froeca/Software-Defined-Radio/Images/Arduino_design.PNG

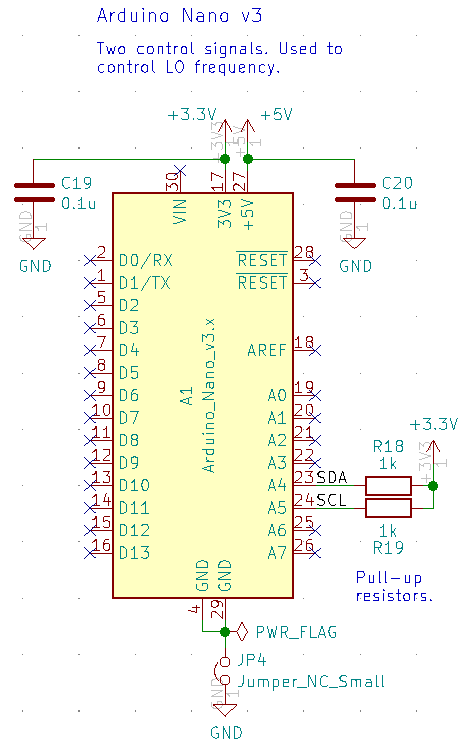
Images/Arduino_design.PNG
