froeca/Software-Defined-Radio/Images/BJT_design_v3a.PNG

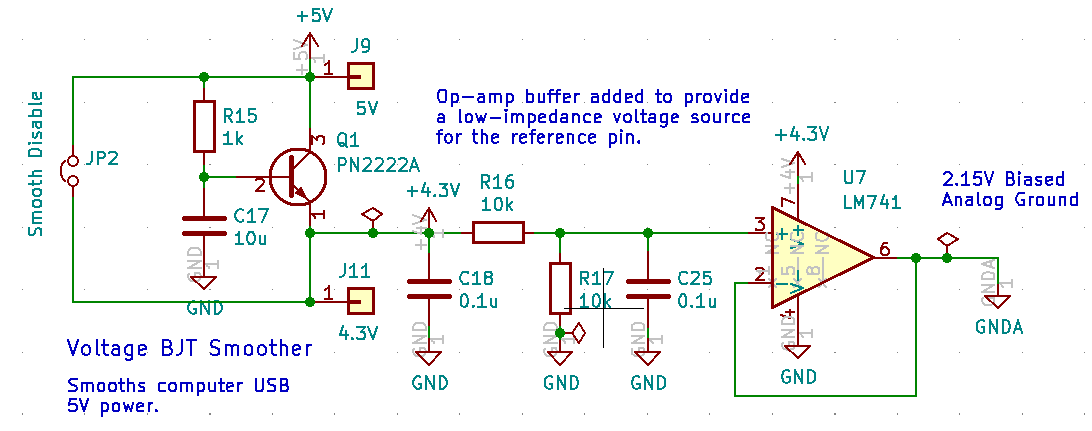
Images/BJT_design_v3a.PNG
