froeca/Software-Defined-Radio/Images/Block_Diagram.png

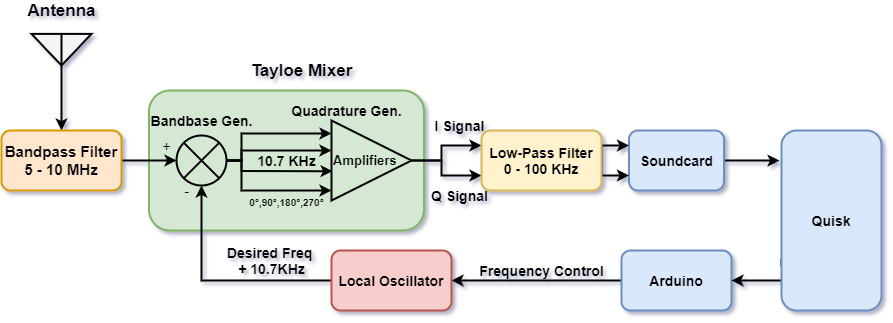
Images/Block_Diagram.png
