froeca/Software-Defined-Radio/Images/BPF_error.png

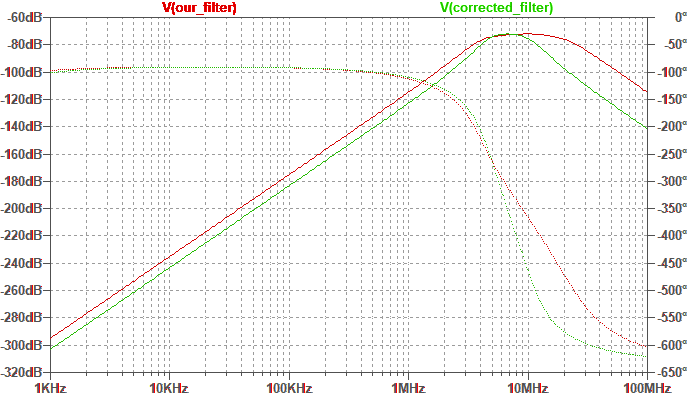
Images/BPF_error.png
