froeca/Software-Defined-Radio/Images/BPF_ideal.PNG

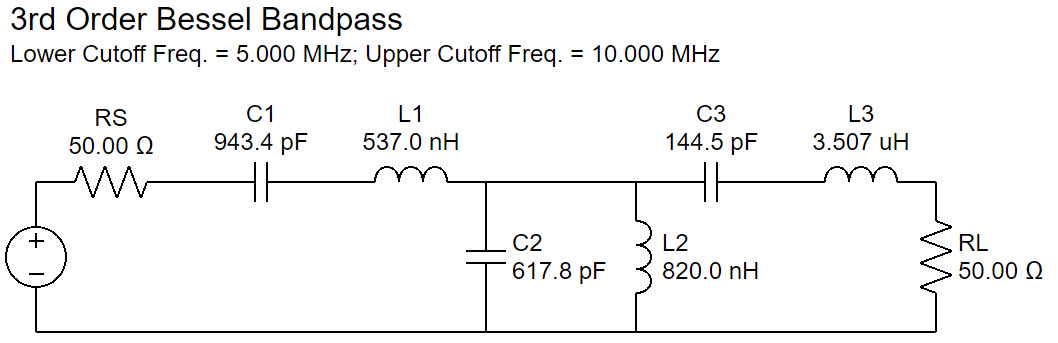
Images/BPF_ideal.PNG
