froeca/Software-Defined-Radio/Images/BPF_response.png

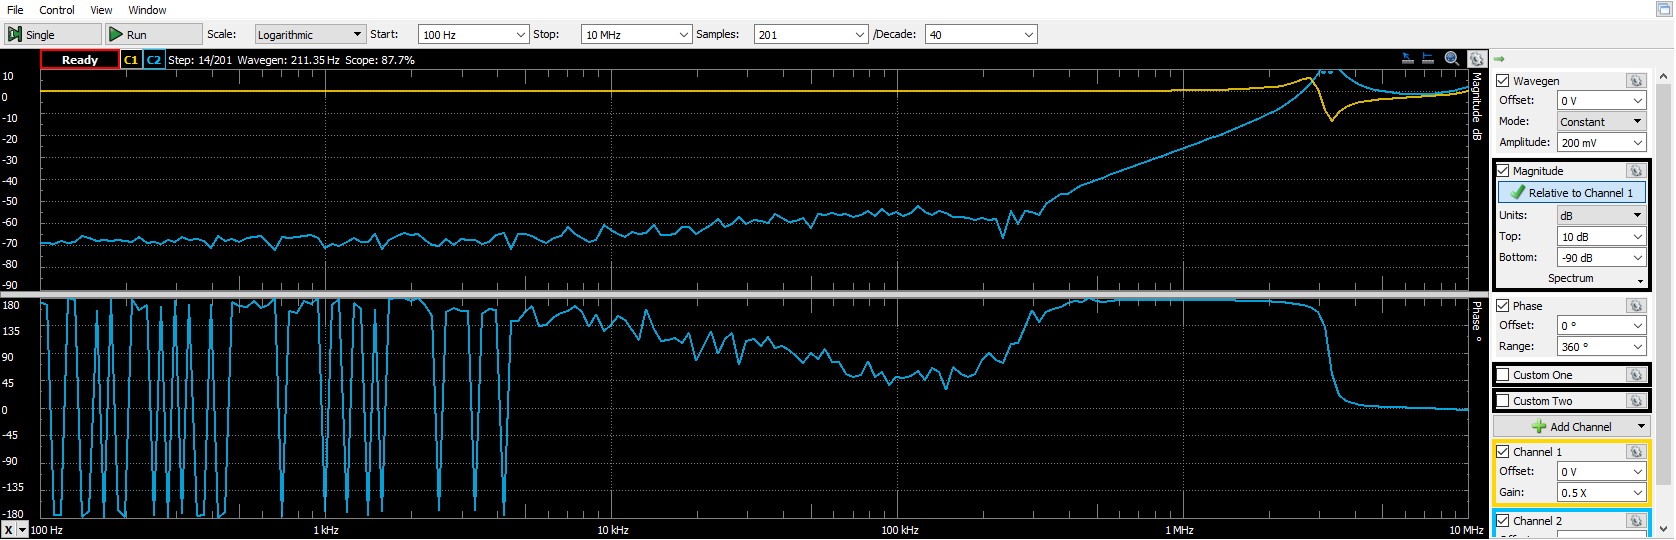
Images/BPF_response.png
