froeca/Software-Defined-Radio/Images/BPF_response_graph.PNG

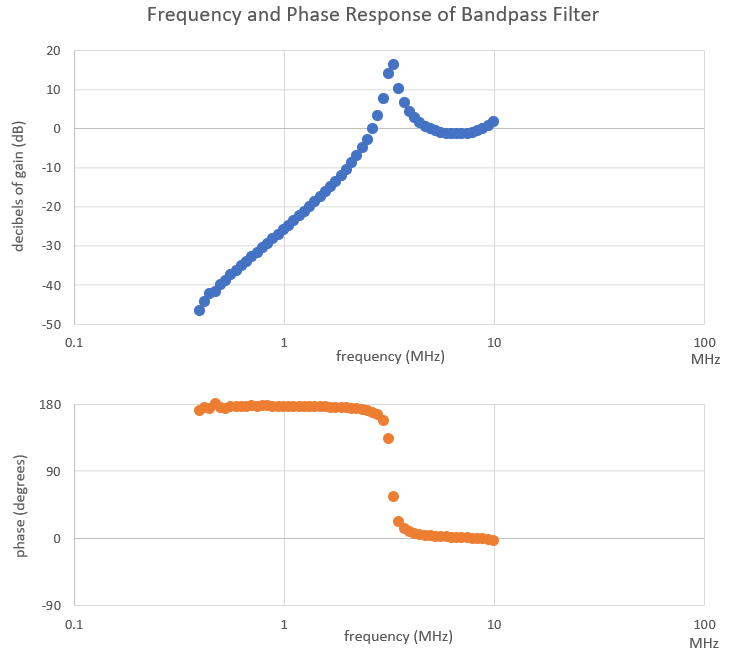
Images/BPF_response_graph.PNG
