froeca/Software-Defined-Radio/Images/Clkgen_response.jpeg

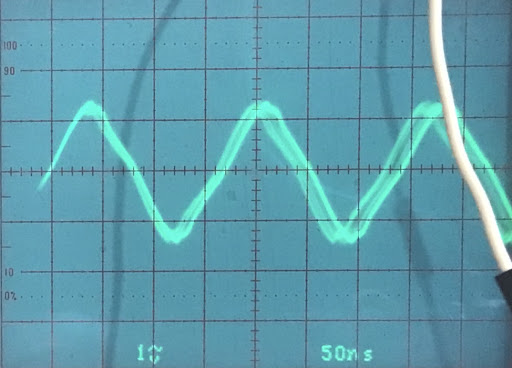
Images/Clkgen_response.jpeg
