froeca/Software-Defined-Radio/Images/Froelich_Reciever_PCB.png

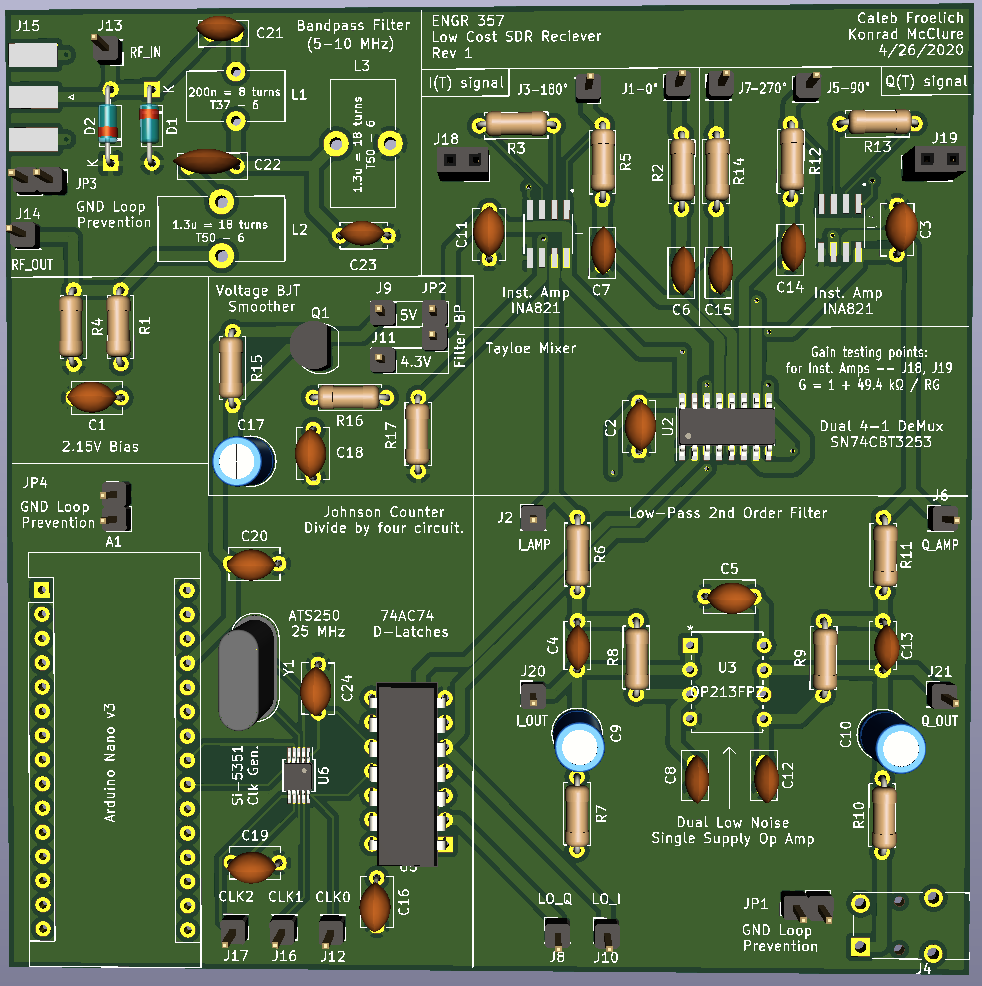
Images/Froelich_Reciever_PCB.png
