froeca/Software-Defined-Radio/Images/Froelich_Reciever_PCB_2.png

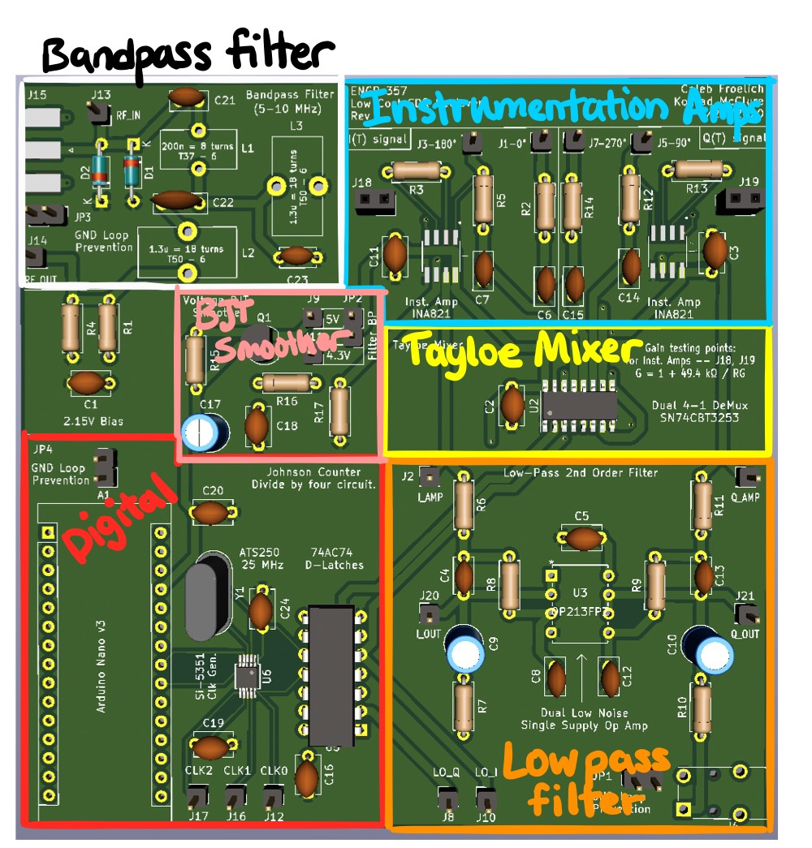
Images/Froelich_Reciever_PCB_2.png
