froeca/Software-Defined-Radio/Images/INA821_response.PNG

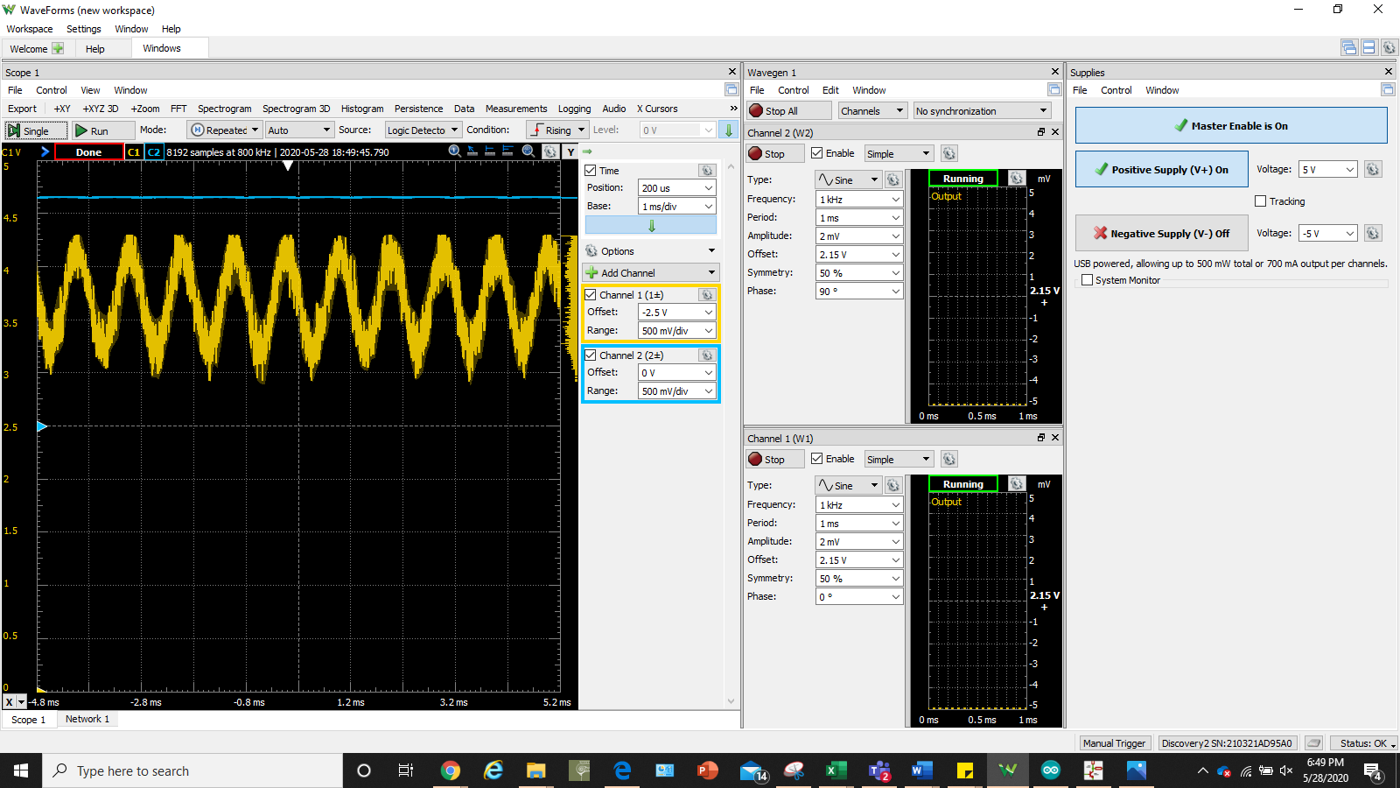
Images/INA821_response.PNG
