froeca/Software-Defined-Radio/Images/JCNTR_design.PNG

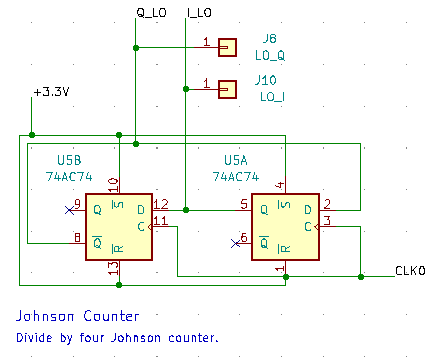
Images/JCNTR_design.PNG
