froeca/Software-Defined-Radio/Images/JCNTR_response2.jpeg

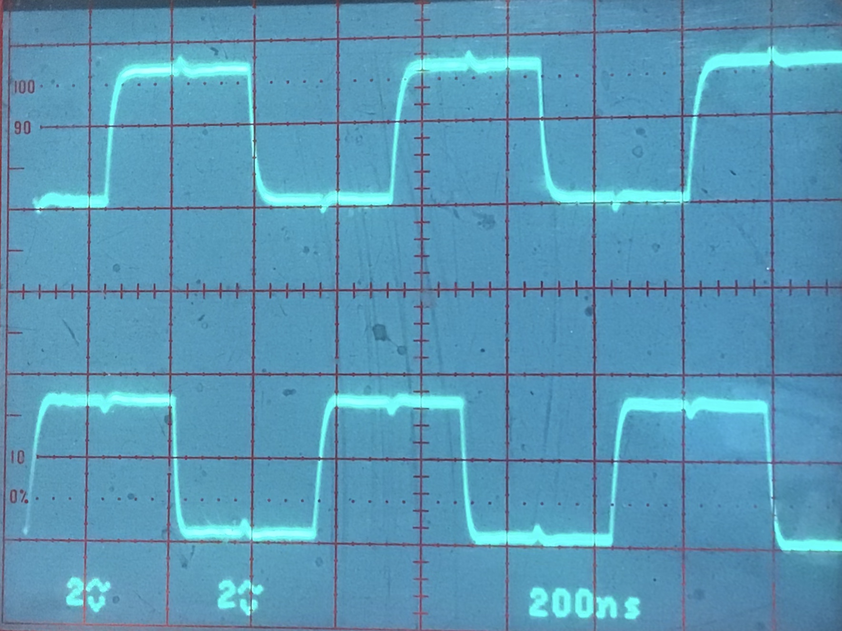
Images/JCNTR_response2.jpeg
