froeca/Software-Defined-Radio/Images/JCNTR_response.png

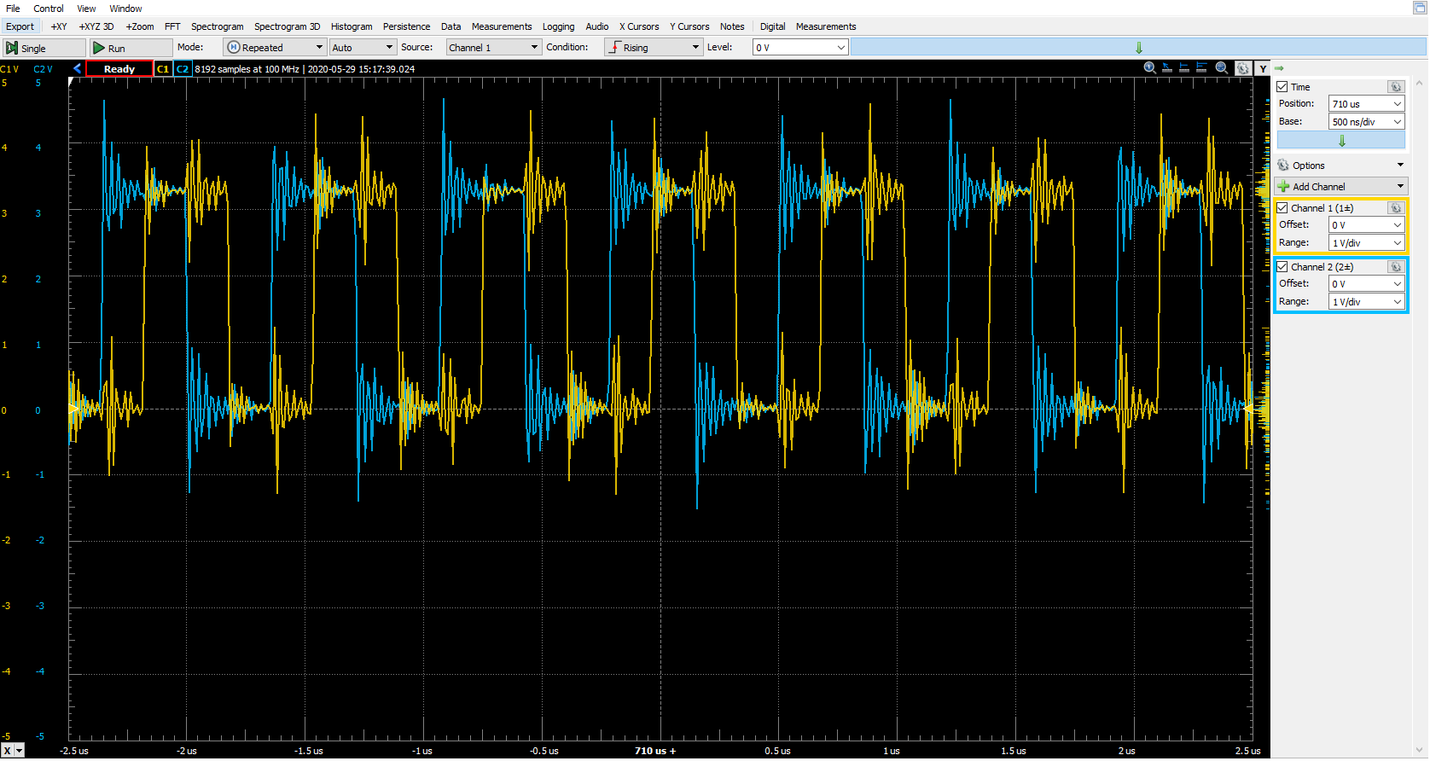
Images/JCNTR_response.png
