froeca/Software-Defined-Radio/Images/LPF_design.PNG

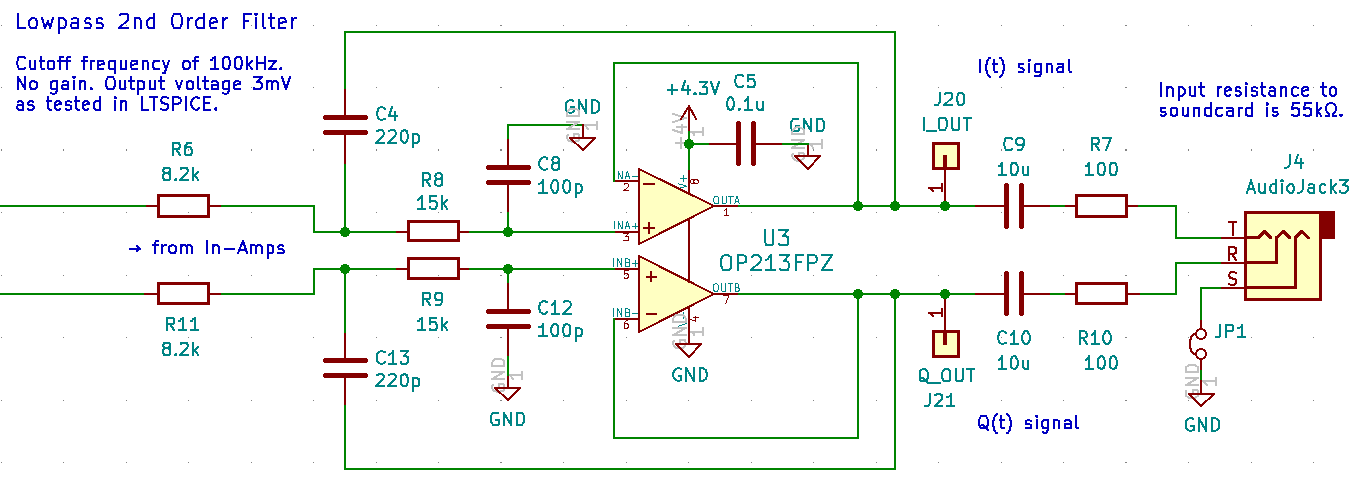
Images/LPF_design.PNG
