froeca/Software-Defined-Radio/Images/LPF_response.png

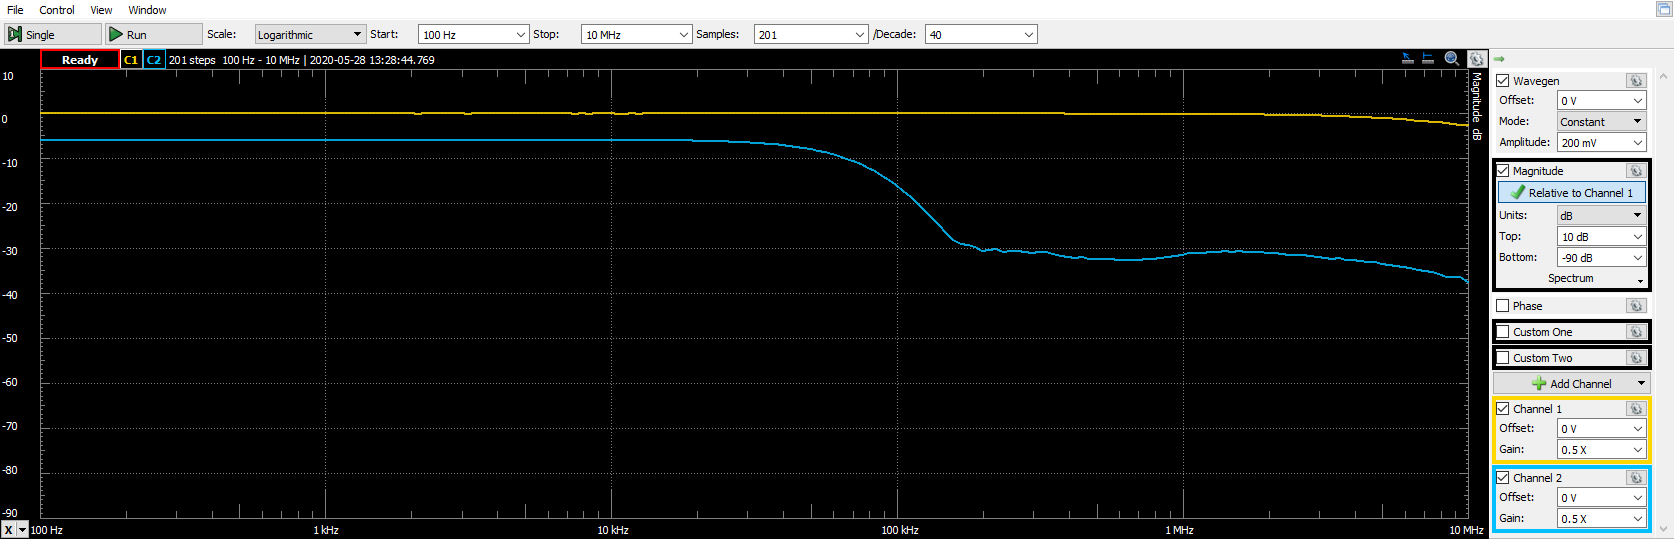
Images/LPF_response.png
