froeca/Software-Defined-Radio/Images/LPF_response_graph.PNG

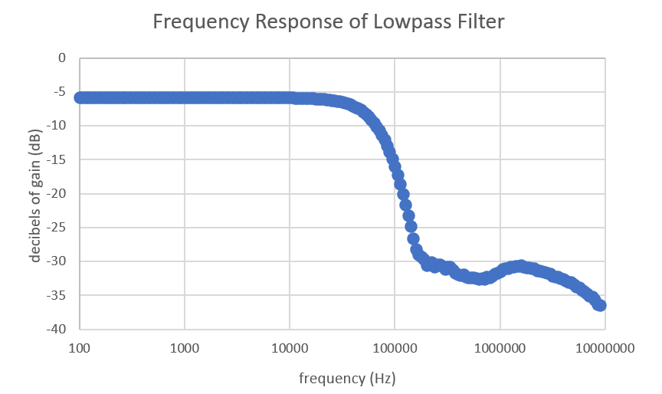
Images/LPF_response_graph.PNG
