froeca/Software-Defined-Radio/Images/Pull-up_Resistors.jpg

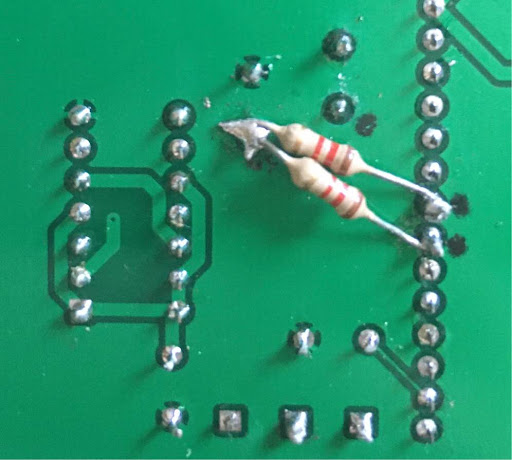
Images/Pull-up_Resistors.jpg
