froeca/Software-Defined-Radio/Images/SDA_SCL.png

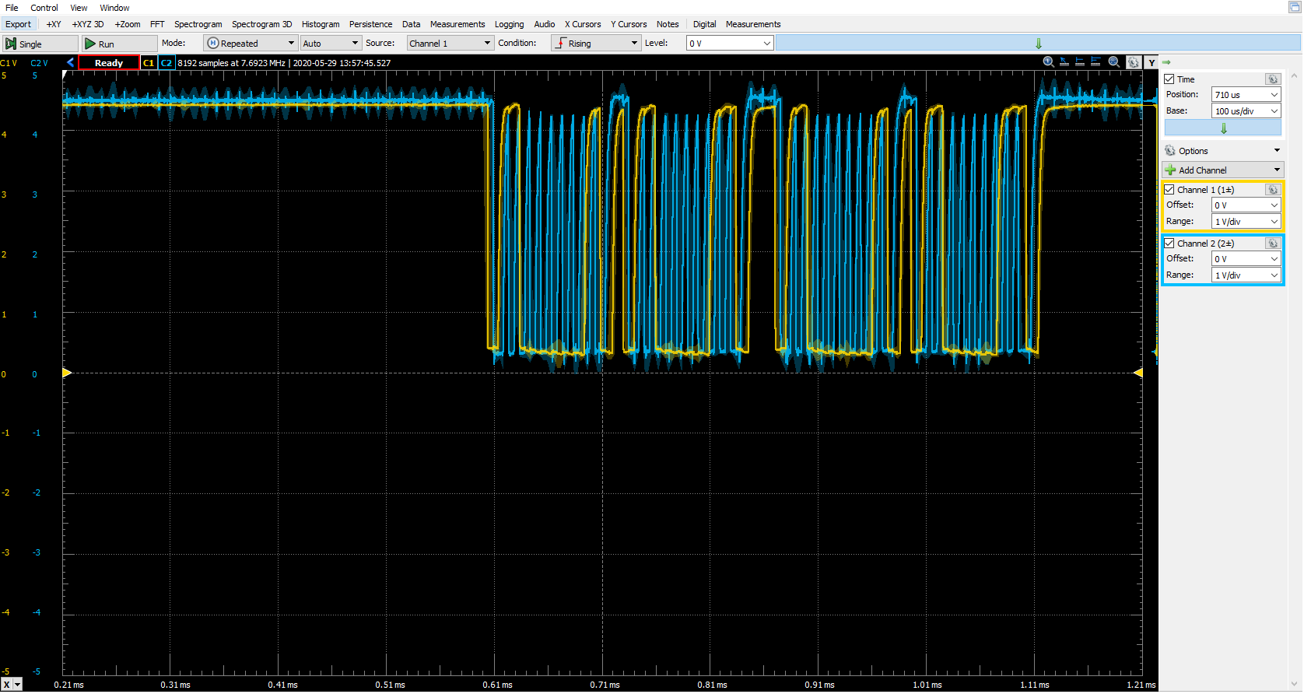
Images/SDA_SCL.png
