froeca/Software-Defined-Radio/Images/Spice_bandpass.PNG

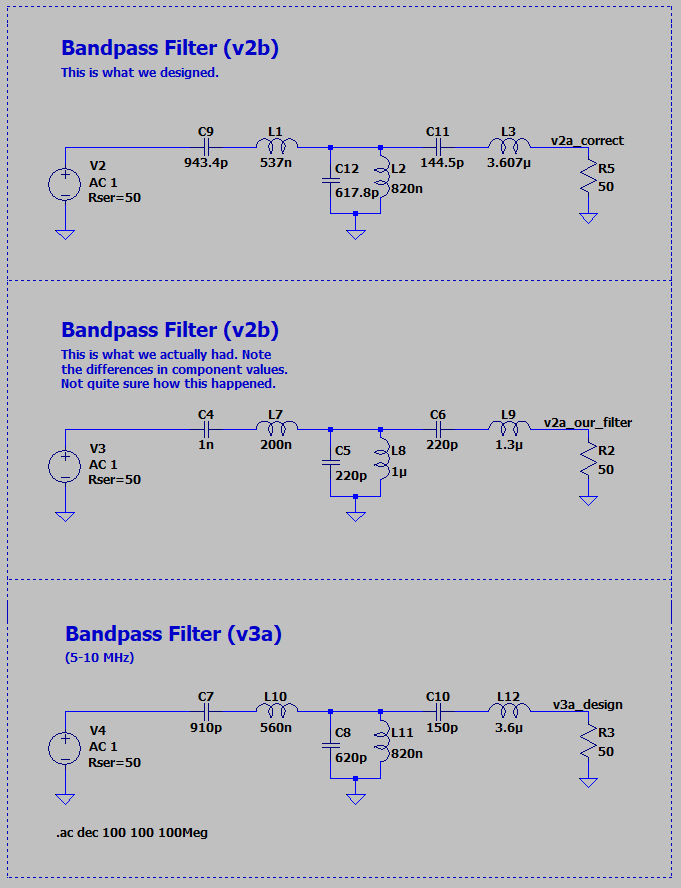
Images/Spice_bandpass.PNG
