froeca/Software-Defined-Radio/Images/Spice_bandpass_v2b.PNG

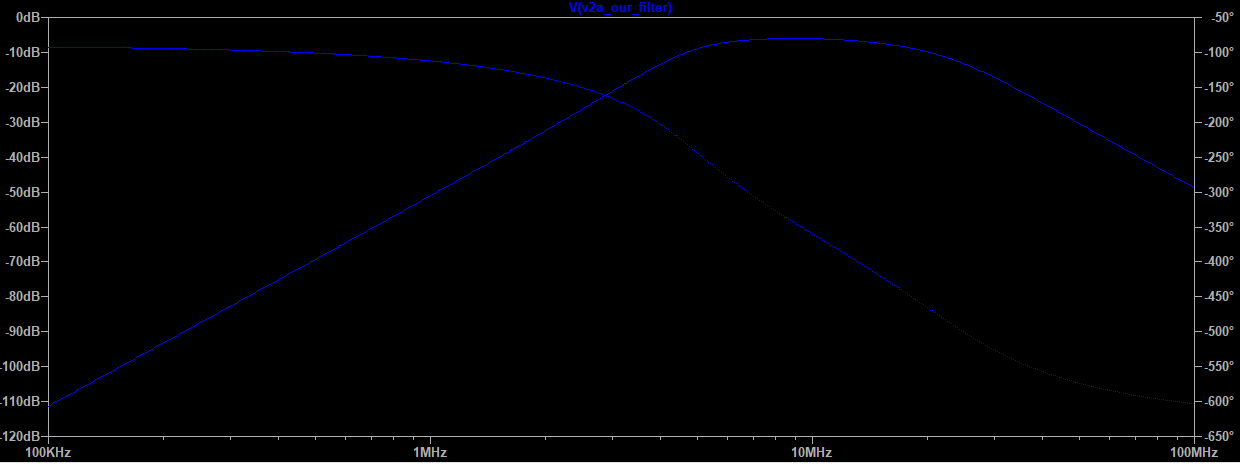
Images/Spice_bandpass_v2b.PNG
