froeca/Software-Defined-Radio/Images/Spice_bandpass_v3a.PNG

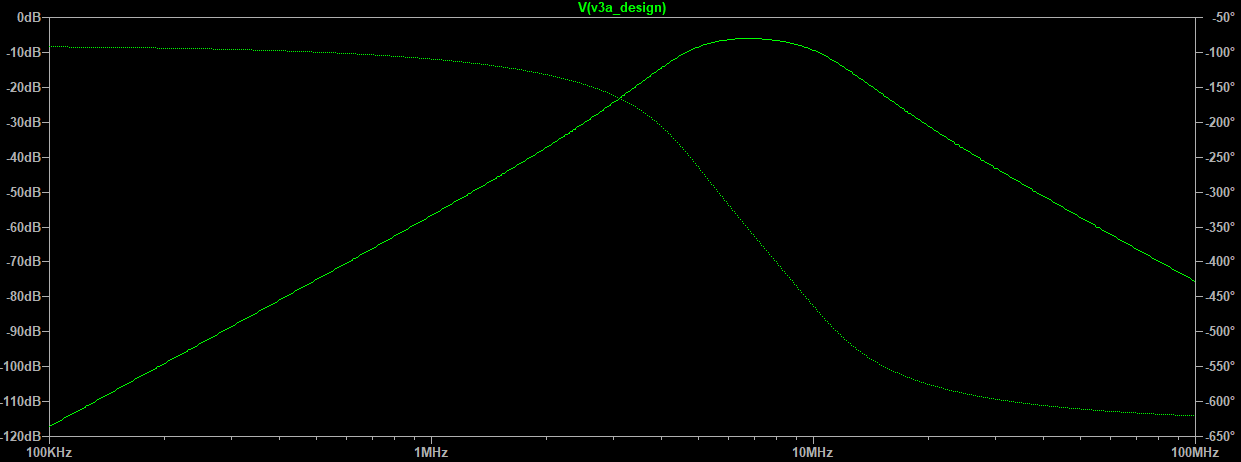
Images/Spice_bandpass_v3a.PNG
