froeca/Software-Defined-Radio/Images/Spice_lowpass.PNG

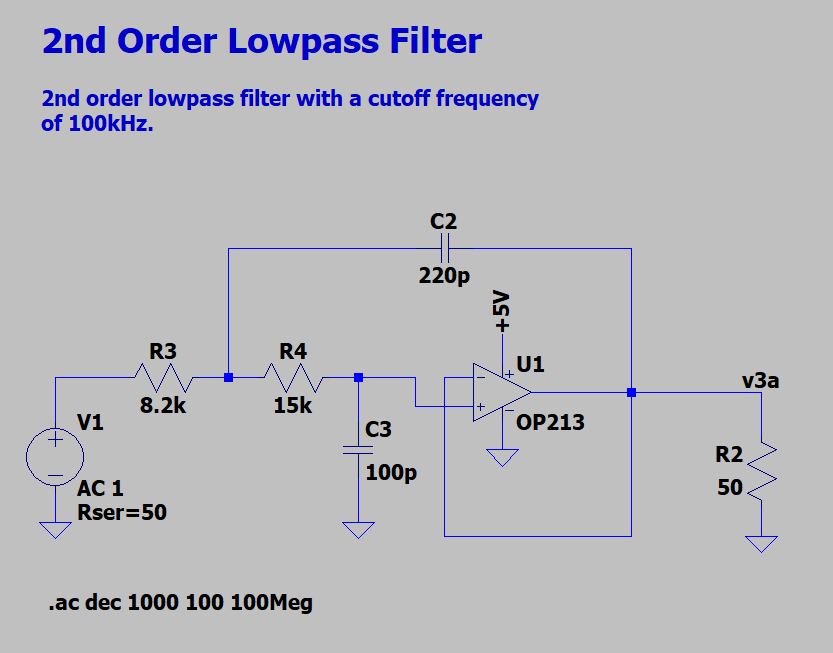
Images/Spice_lowpass.PNG
