froeca/Software-Defined-Radio/Images/Spice_lowpass_v3a.PNG

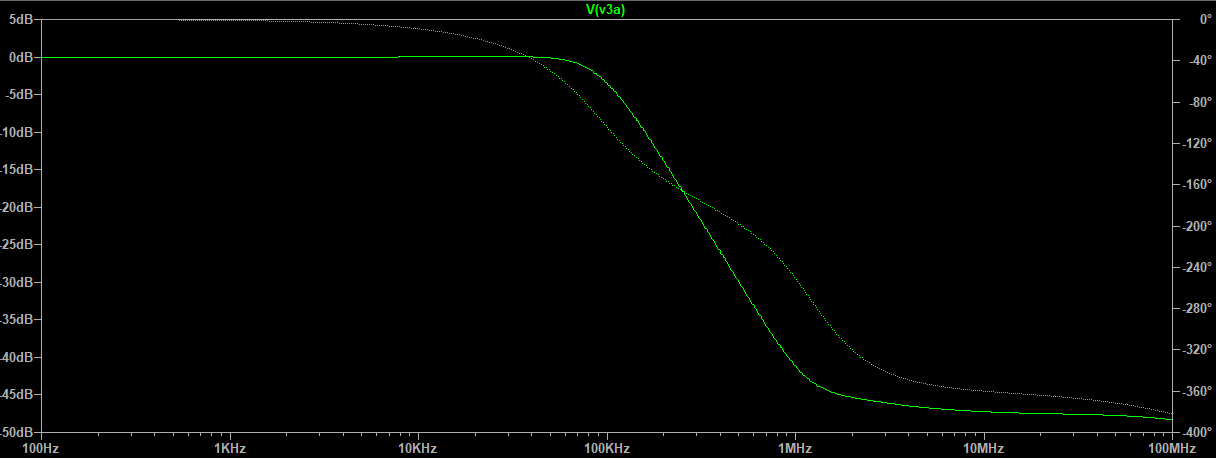
Images/Spice_lowpass_v3a.PNG
