froeca/Software-Defined-Radio/Images/Spice_v2b_full.PNG

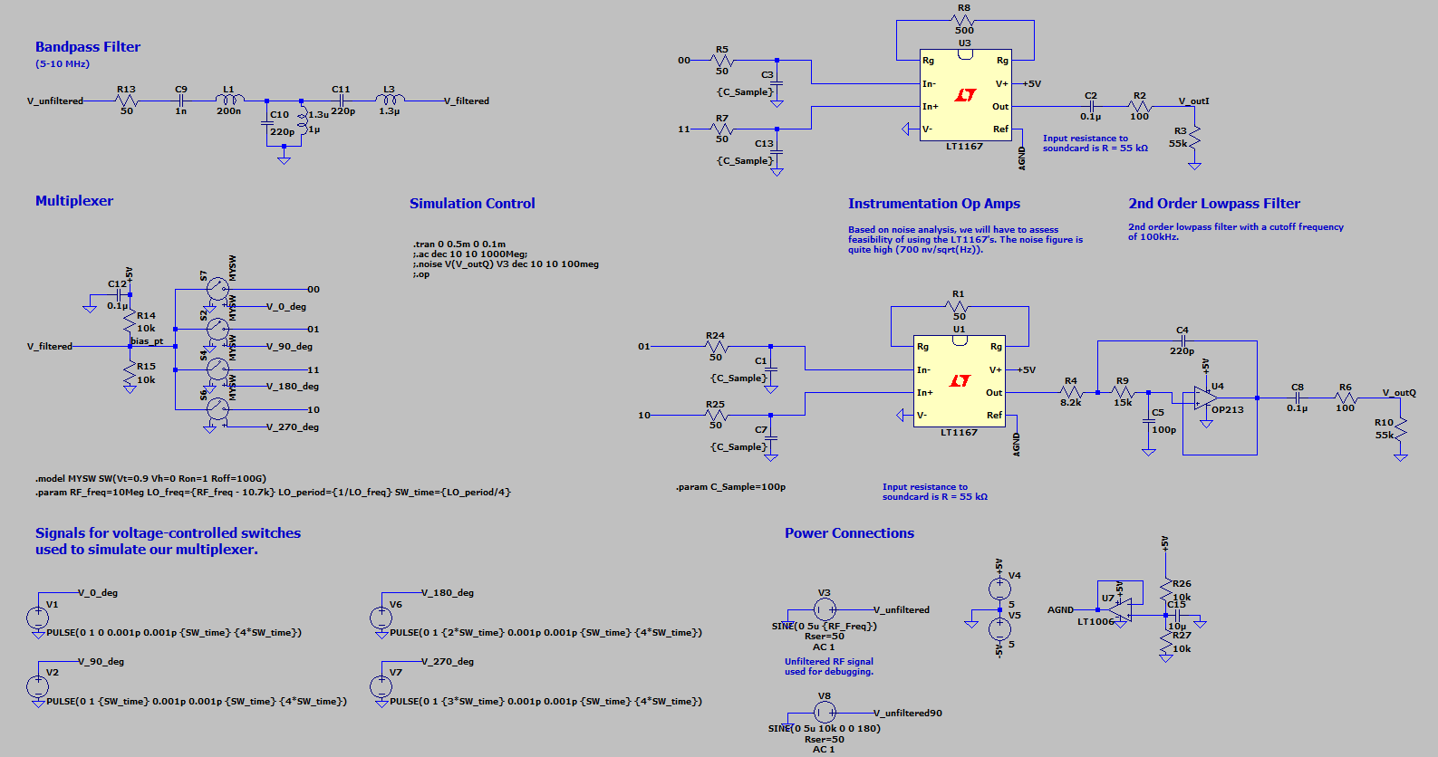
Images/Spice_v2b_full.PNG
