froeca/Software-Defined-Radio/Images/Spice_v2b_IandQ.png

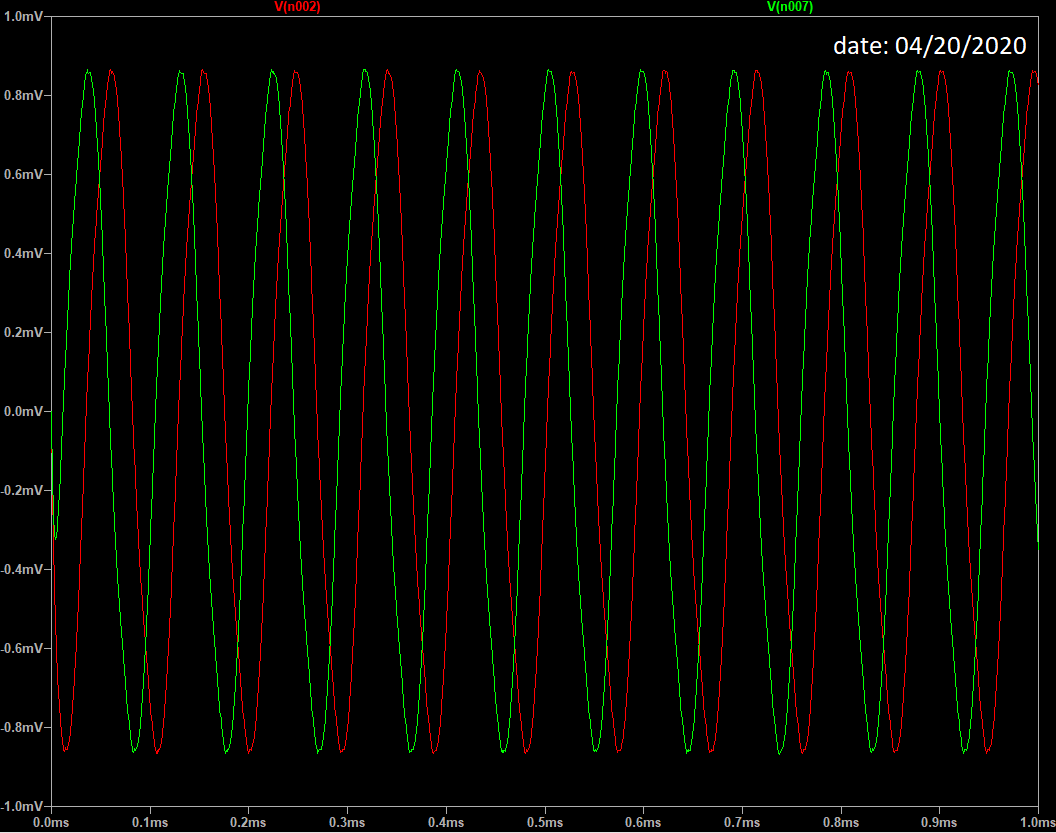
Images/Spice_v2b_IandQ.png
