froeca/Software-Defined-Radio/Images/Spice_v2b_INA821.png

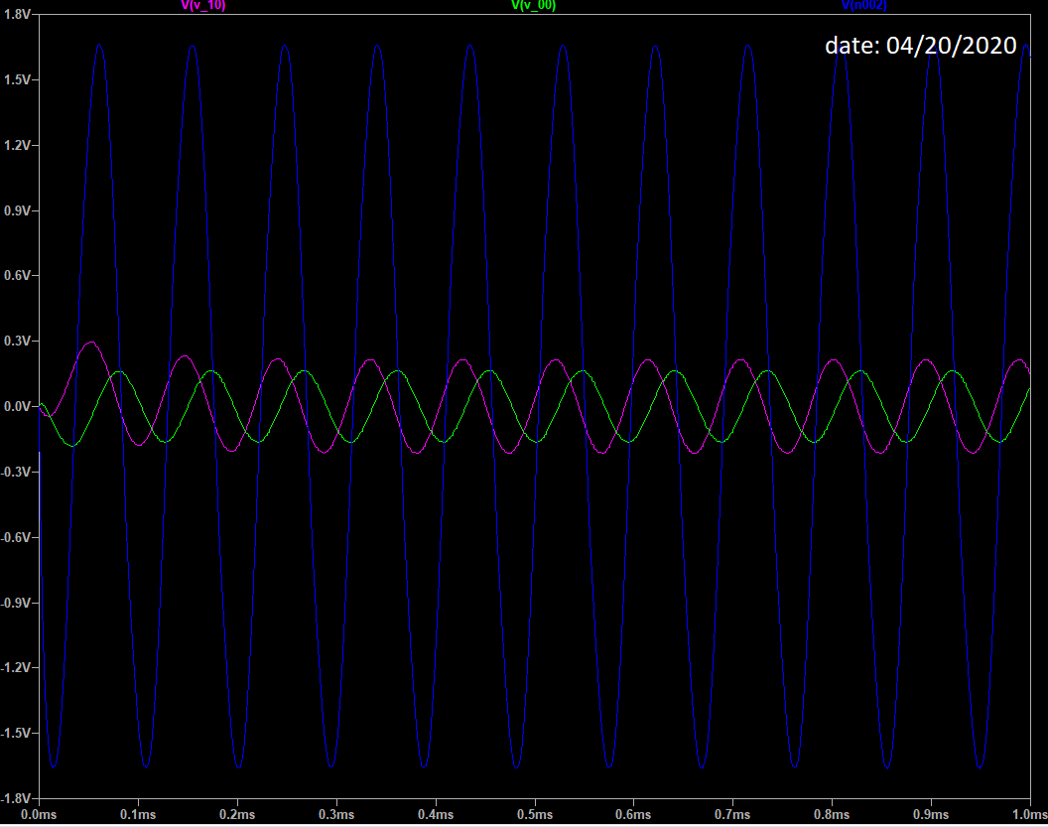
Images/Spice_v2b_INA821.png
