froeca/Software-Defined-Radio/Images/Spice_v2b_messy.png

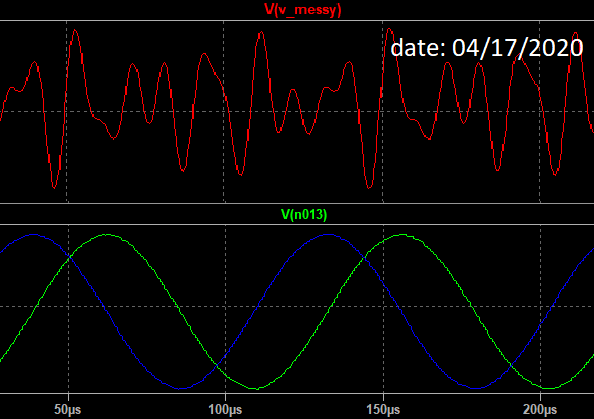
Images/Spice_v2b_messy.png
