froeca/Software-Defined-Radio/Images/TMIX_design.PNG

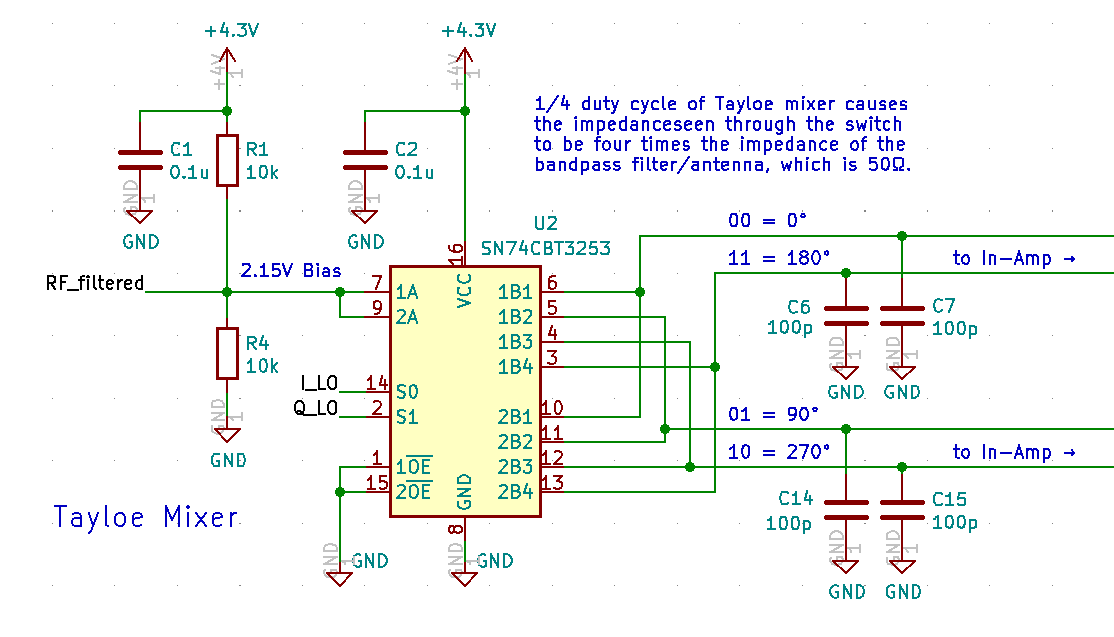
Images/TMIX_design.PNG
