froeca/Software-Defined-Radio/Images/TMIX_theory.jpeg

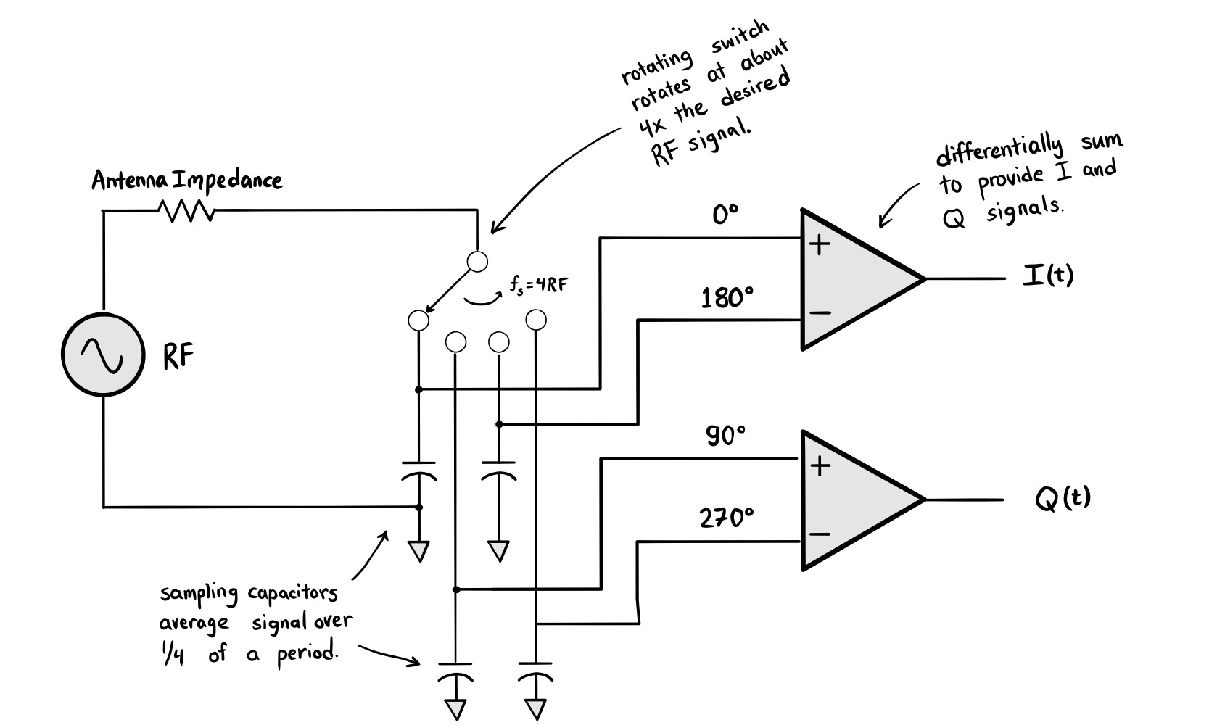
Images/TMIX_theory.jpeg
