froeca/Software-Defined-Radio/BOMs/Parts_list.PNG

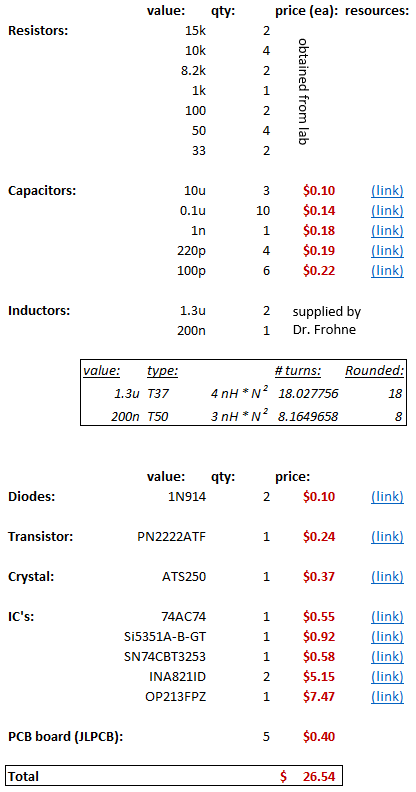
BOMs/Parts_list.PNG
