froeca/Software-Defined-Radio/Images/issue_CMMRofINA821.PNG

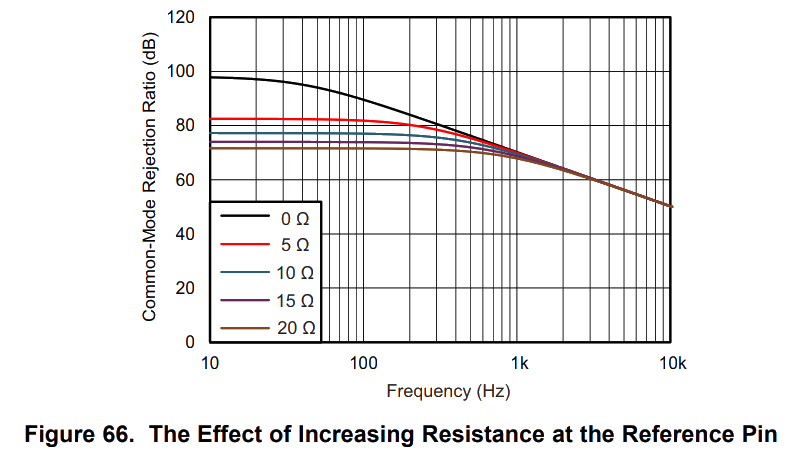
Images/issue_CMMRofINA821.PNG
