froeca/Software-Defined-Radio/Images/issue_DCbiaspt.png

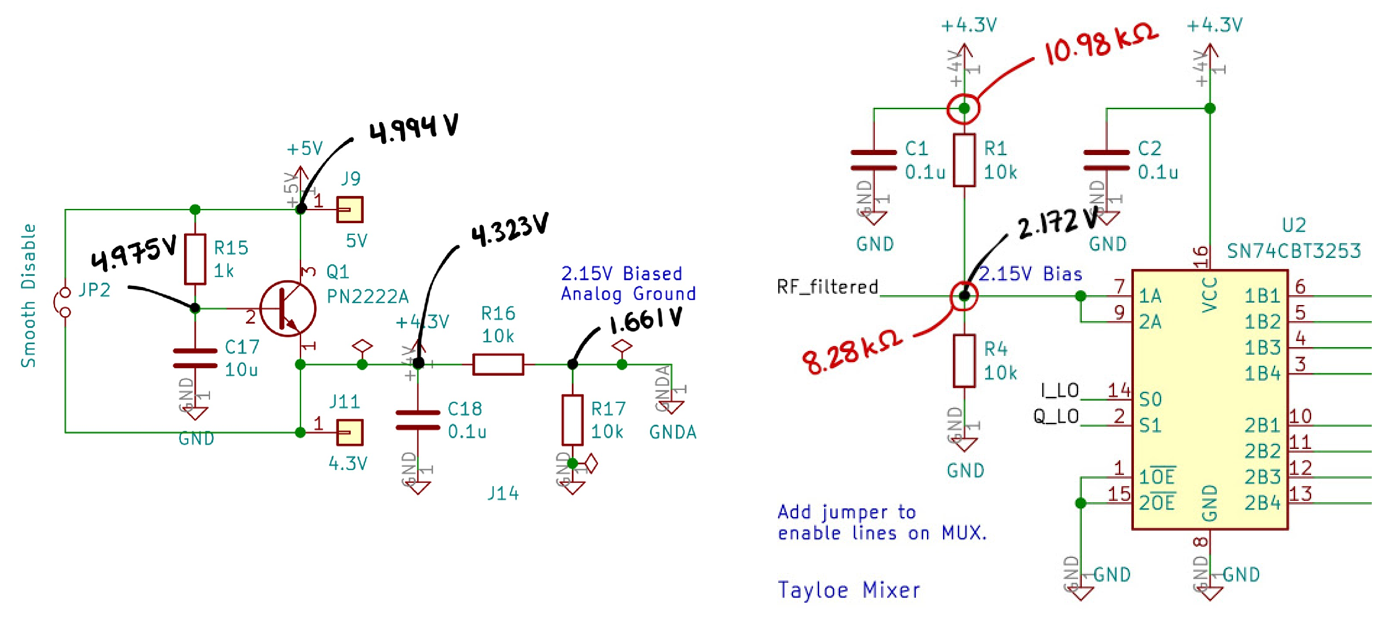
Images/issue_DCbiaspt.png
