froeca/Software-Defined-Radio/Images/issue_INA821internal.PNG

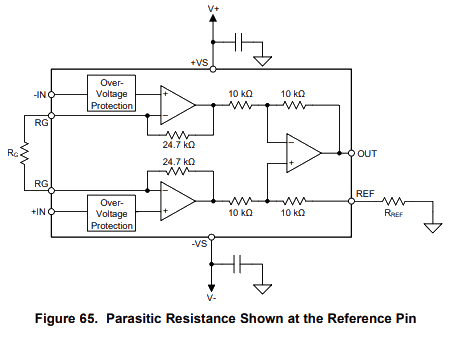
Images/issue_INA821internal.PNG
