froeca/Software-Defined-Radio/Attenuator_Design/LTSPICE_Simulations/AttentuatorDesign.asc

C1: cap; 0.167p
C2: cap; 0.167p
C3: cap; 0.167p
C4: cap; 0.167p
C5: cap; 0.167p
C6: cap; 0.167p
C7: cap; 0.167p
C8: cap; 0.167p
C9: cap; 0.167p
C10: cap; 0.167p
R1: res; 50
R2: res; 15
R3: res; 360
R4: res; 180
R5: res; 30
R6: res; 180
R7: res; 91
R8: res; 75
R9: res; 91
R10: res; 62
R11: res; 240
R12: res; 62
R13: res; 51
R14: res; 2700
R15: res; 360
R16: res; 51
R17: res; 50
R18: res; 360
R19: res; 15
R20: res; 360
R21: res; 180
R22: res; 30
R23: res; 180
R24: res; 91
R25: res; 75
R26: res; 91
R27: res; 62
R28: res; 240
R29: res; 62
R30: res; 51
R31: res; 2700
R32: res; 51
R33: res; 50
V1: voltage; SINE(0 10m 100k 0); AC 10m 0
V2: voltage; 10
Named nets: 0, Vin, Vout
;tran 0 0.5m 0 10u
;ac dec 100 1m 100Meg
.op
