froeca/Software-Defined-Radio/Attenuator_Design/LTSPICE_Simulations/AttentuatorDesign2.asc

C1: cap; 0.167p
C2: cap; 0.167p
C3: cap; 0.167p
C4: cap; 0.167p
C5: cap; 0.167p
C6: cap; 0.167p
C7: cap; 0.167p
C8: cap; 0.167p
C9: cap; 0.167p
C10: cap; 0.167p
L1: ind; 10m
R1: res; 50
R2: res; 348
R3: res; 14.7
R4: res; 348
R5: res; 178
R6: res; 30
R7: res; 178
R8: res; 95.3
R9: res; 71.5
R10: res; 95.3
R11: res; 61.9
R12: res; 249
R13: res; 61.9
R14: res; 51.1
R15: res; 2.49k
R16: res; 51.1
R17: res; 50
R18: res; 348
R19: res; 14.7
R20: res; 348
R21: res; 178
R22: res; 30
R23: res; 178
R24: res; 95.3
R25: res; 71.5
R26: res; 95.3
R27: res; 61.9
R28: res; 249
R29: res; 61.9
R30: res; 51.1
R31: res; 2.49k
R32: res; 51.1
V1: voltage; SINE(0 10m 100k 0); AC 10m 0
V2: voltage; 10
Named nets: 0, Vin, Vout
;tran 0 0.5m 0 10u
.ac dec 100 1m 100Meg
