froeca/Software-Defined-Radio/LTSPICE_Simulations/LowpassFilterSimulation.asc

C2: cap; 220p
C3: cap; 100p
R2: res; 50
R3: res; 8.2k
R4: res; 15k
U1: OP213
V1: voltage; ""; AC 1; Rser=50
V2: voltage; 5
Named nets: 0, v3a, +5V
2nd Order Lowpass Filter
2nd order lowpass filter with a cutoff frequency 
of 100kHz.
.ac dec 1000 100 100Meg
