froeca/Software-Defined-Radio/LTSPICE_Simulations/BandpassFilterSimulations.asc

C4: cap; 1n
C5: cap; 220p
C6: cap; 220p
C7: cap; 910p
C8: cap; 620p
C9: cap; 943.4p
C10: cap; 150p
C11: cap; 144.5p
C12: cap; 617.8p
L1: ind; 537n
L2: ind; 820n
L3: ind; 3.607µ
L7: ind; 200n
L8: ind; 1µ
L9: ind; 1.3µ
L10: ind; 560n
L11: ind; 820n
L12: ind; 3.6µ
R2: res; 50
R3: res; 50
R5: res; 50
V2: voltage; ""; AC 1; Rser=50
V3: voltage; ""; AC 1; Rser=50
V4: voltage; ""; AC 1; Rser=50
Named nets: 0, v2a_correct, v2a_our_filter, v3a_design
Bandpass Filter (v2b)
This is what we designed.
Bandpass Filter (v2b)
This is what we actually had. Note 
the differences in component values.
Not quite sure how this happened.
Bandpass Filter (v3a)
.ac dec 1000 100k 100Meg
(5-10 MHz)
